kaveenkumar/SmartAgriculture/PPT Files/SA BLOCK DIAGRAM.pptx

INTERNET

USB

INPUT
SENSOR PORTS

RTC

RELAY

SIM900
GSM MODULE

16x2 LCD DISPLAY

ARM CORTEX M0

TARANG F4 ZIGBEE MODULE

Serial
Debugger

Opto
Coupler

POWER MANAGEMENT

INPUT SUPPLY
