kaveenkumar/SmartAgriculture/PPT Files/SA.pptx

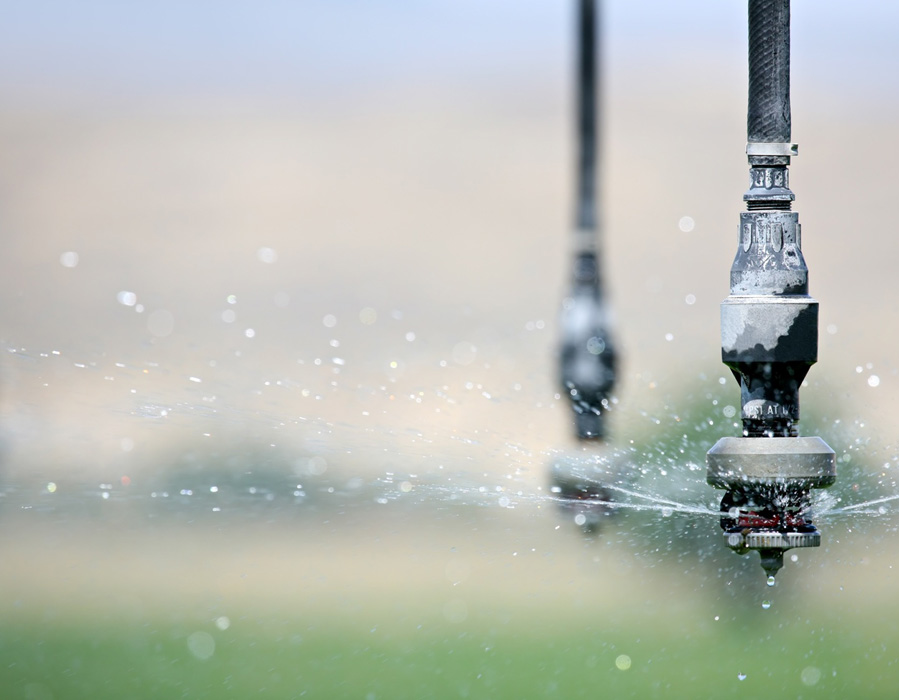
[picture p43: figure]

B.M.S COLLEGE OF ENGINEERING
Basavanagudi, Bangalore - 560 019, Karnataka, India
DEPARTMENT OF ELECTRONICS & OMMUNICATION

PROJECT PRESENTATION ON
“PRECISION AGRICULTURE”

1. Hemantha Gowda C.V. - 1BM11EC406 3. NIKHILESH.R - 1BM09IT017
2. KIRAN.M - 1BM09IT014 4. S.M.SALMAN - 1BM09IT025

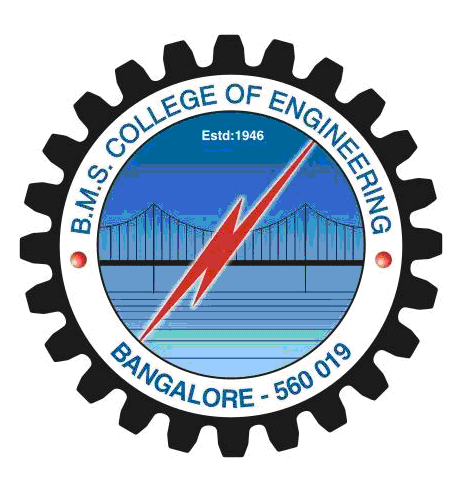
[picture p44: figure]

Project By:

## HISTORY

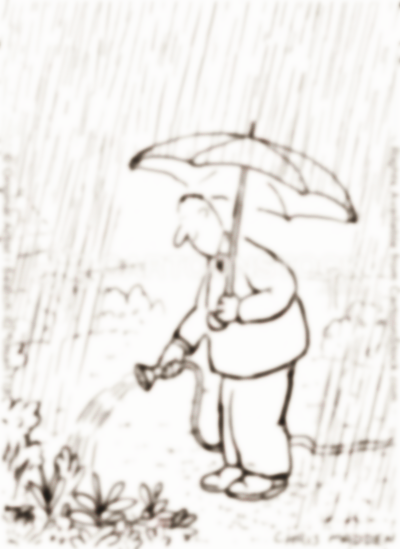
[picture p45: figure]

Agriculture being the Indian economy's strong-hold unfortunately suffers for the carelessness of its cultivators. Its high time we realized our responsibilities & worked towards the upliftment of the society.

## WHY?

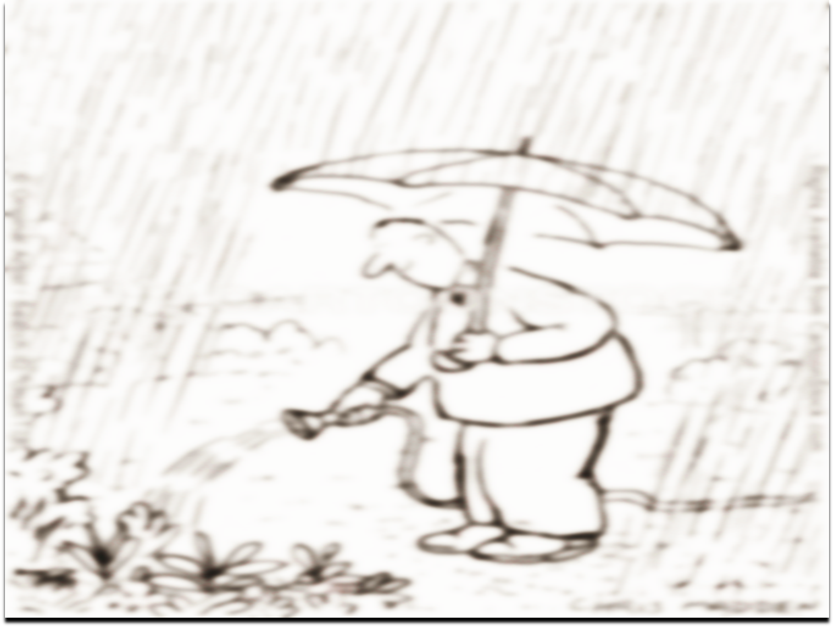
[picture p46: figure]

No remote Data Acquisition System in the present world is perfect until it remains effective and lasts for a pre-determined amount of time. The proposed Low Power Data Acquisition system proves to be advantageous in both the degrees.

## Slide 4

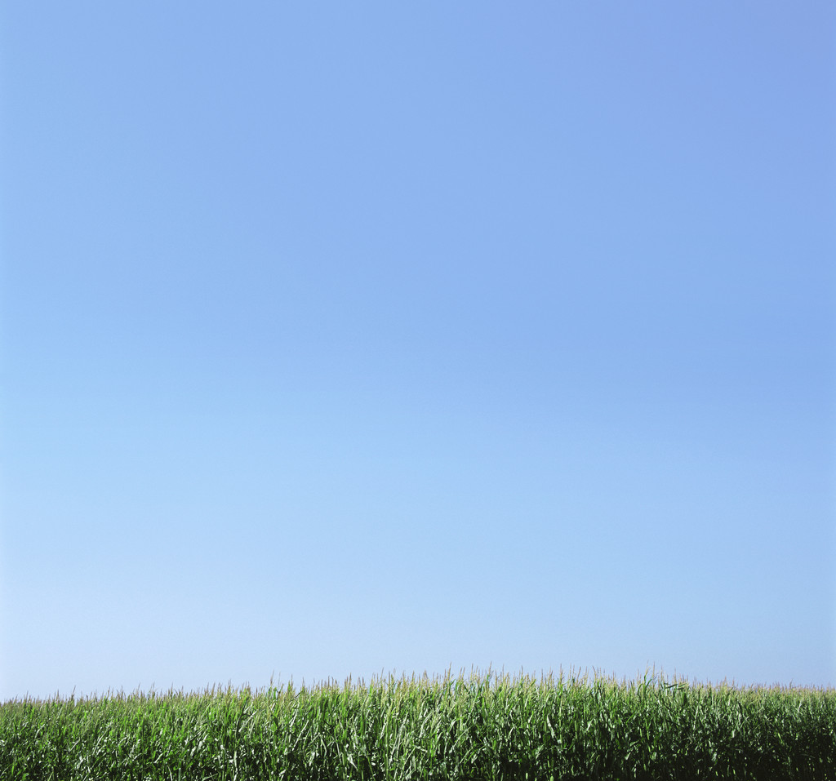
[picture p47: figure]

BLOCK DIAGRAM OVERVIEW

REMOTE
STATION

REMOTE
STATION

REMOTE
STATION

BASE
STATION

GPRS

SERVER

REMOTE
STATION

REMOTE
STATION

## Slide 5

BASE STATION

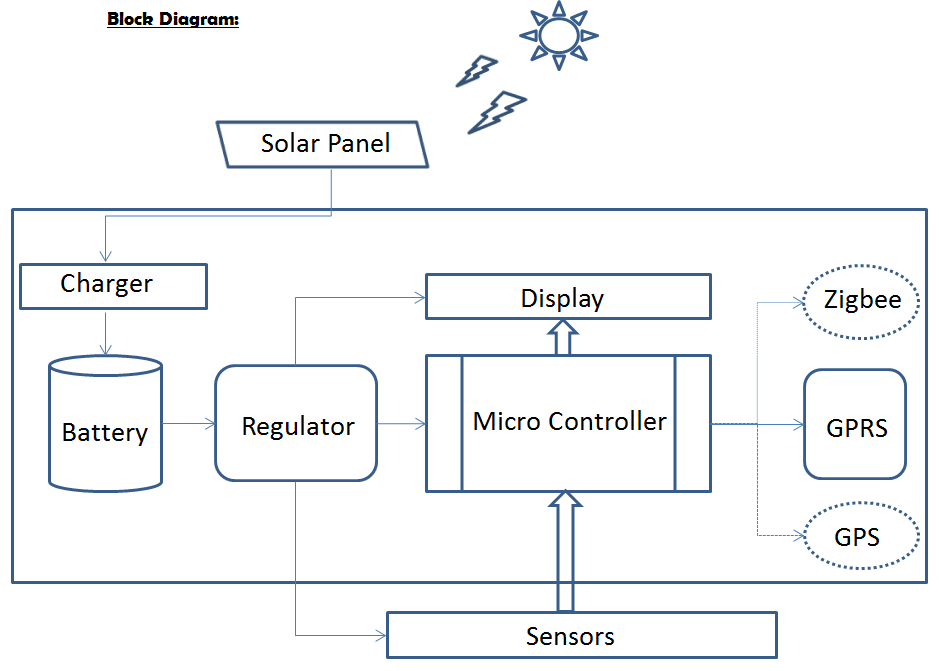
[picture p48: figure]

## COMPONENTS EMPLOYED

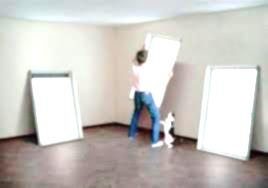
[picture p49: figure]

- ARM Cortex M0
- SIM900
- Relay & Opto-Coupler
- 16x2 Display
- Sensors
- Solenoid Valve
- Misc.

## PROS & CONS

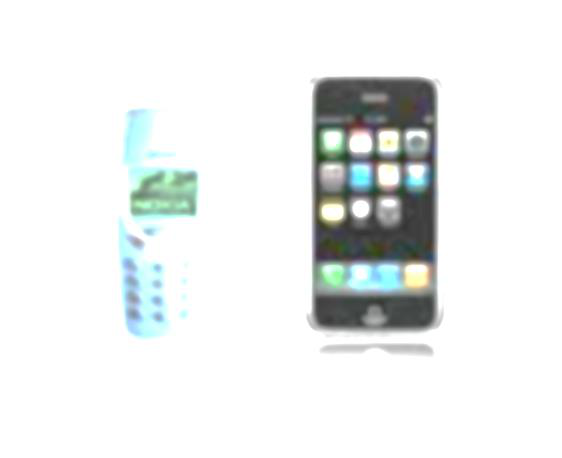
[picture p50: figure]

- Low power
- More advantages
- Less disadvantages

## Conclusion

Mutual investments are subject to market risk. Please read the offer documents carefully before investing.!
