kaveenkumar/SmartAgriculture/PPT Files/Smart Agriculture ppt.pptx

SMART AGRICULTURE

By

Technology At Farms…

Kaveen
Prathap
Nikhil
Hemanth

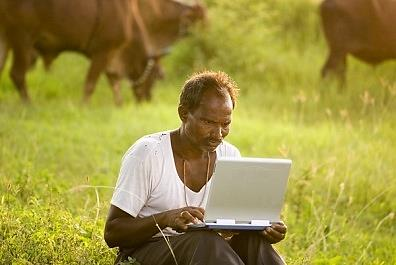
[picture p51: figure]

Guide

Harish V Mekali

## Slide 2

Why?

Optimum Water, More Yield…

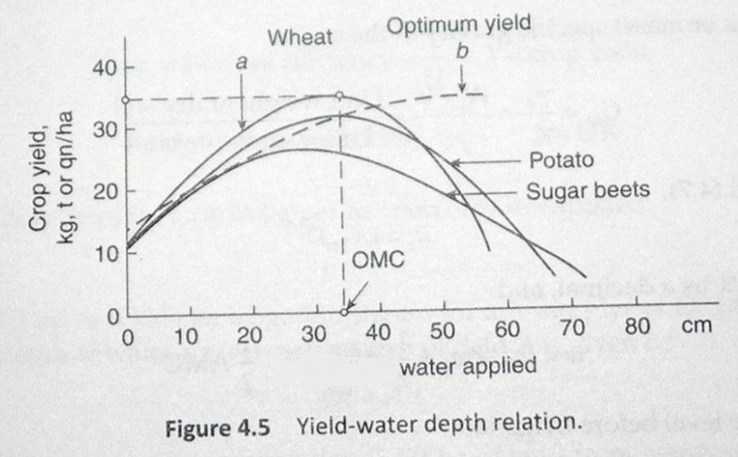
[picture p52: figure]

## Slide 3

Initialization…

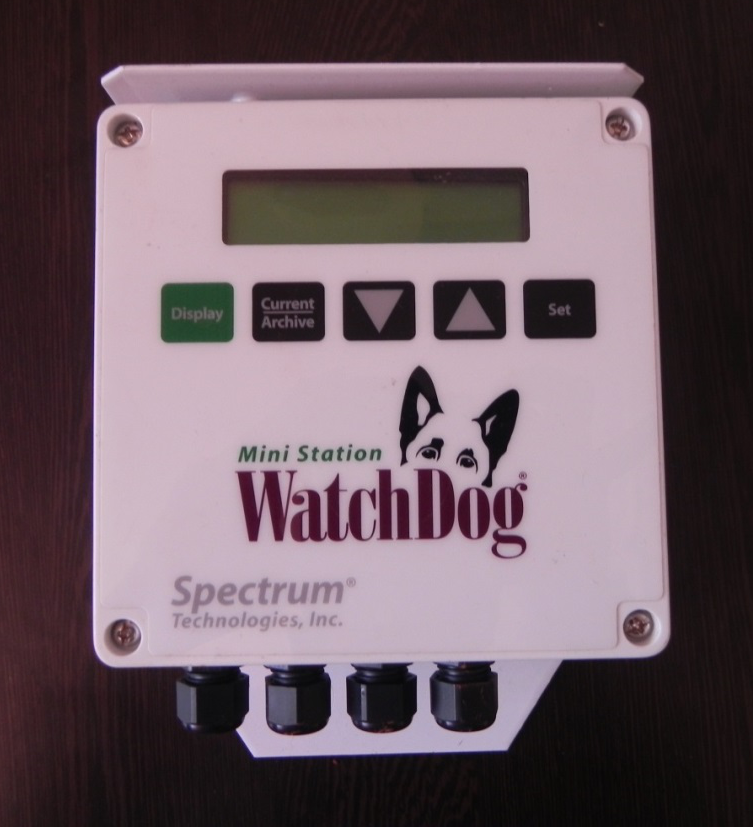
[picture p53: figure]

WatchDog

Sensors
4 Soil moisture sensors (SM100)

Data logger
Exclusive LCD Display confirms logger operation and provides current sensor readings. 0

Data transfer
USB to Serial for connecting to your Laptop

## Slide 4

Improvisation…


Base end

Weather Monitoring
system

Sensor values read

Read values sent

Received values at the user’s hands


User end

Temp:29⁰C SM:25% ST:18⁰C Lum:100lux RH:20%

SMS Format

## Slide 5

Conceptual Block

REMOTE
STATION

REMOTE
STATION

REMOTE
STATION

BASE
STATION

GPRS

SERVER

REMOTE
STATION

REMOTE
STATION

## Slide 6

Base Station…

Battery

Internet

––––

GPRS

Relay

Display

Sensors

ARM Cortex

Memory

## Slide 7

Components…

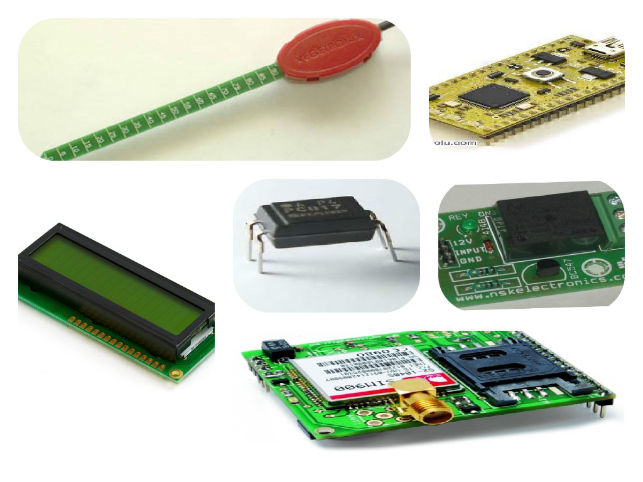
[picture p54: figure]

## Slide 8

Remote Data Acquisition…


The web-link is: http://bmsems.org/new

## Slide 9

Welcome Page…

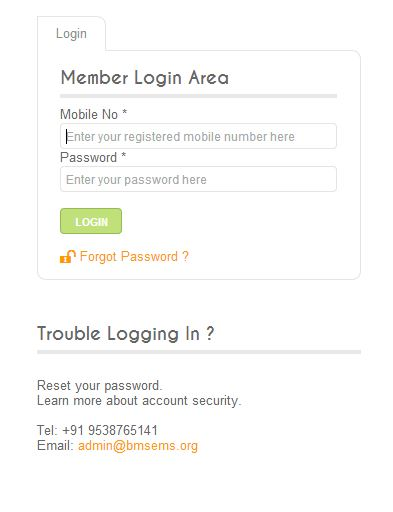
[picture p55: figure]

- Each user is provided with his own distinct ID & a secret password through which he can access the required data.

This way both authentication of the identity and confidentiality of the data is maintained

## Slide 10

User Page…


The user has to login to the website as a member to access the data or use the website to read the parameter he wishes to get a hold on. For this he has to obtain the permission from the administrator.

## Slide 11

Data Page..


Initially we enter the information about soil type, crop and the date of plantation. This information is automatically updated to the database and based on this information our device controls the situation.

## Slide 12

Graph

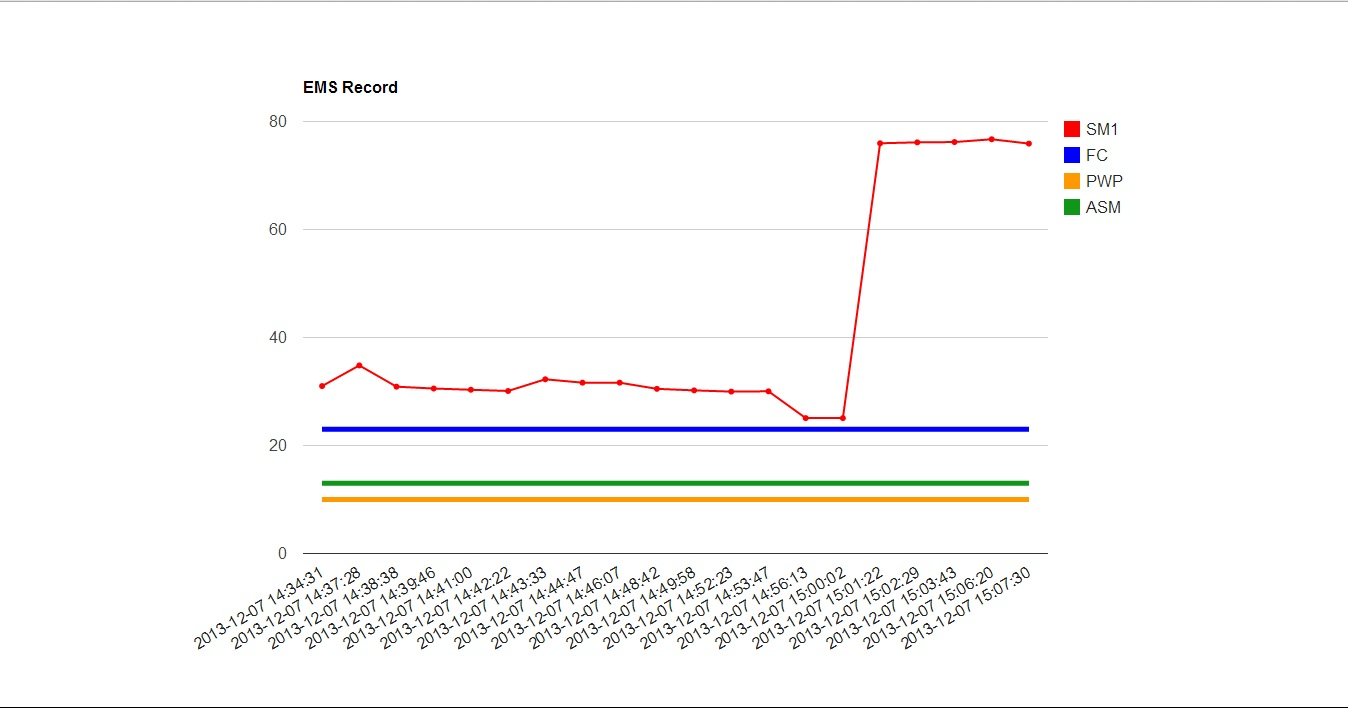
[picture p56: figure]

A graph displays the various sensor values employed, in detail and the output crop details along with the current battery percentage remaining.

## Slide 13

Excel Spreadsheet…


The various sensor data are collectively stored in an excel sheet which can be used later to analyse. The excel files are maintained in an archive format so that less capacity holds maximum amount of information.

## Slide 14

Working Model…

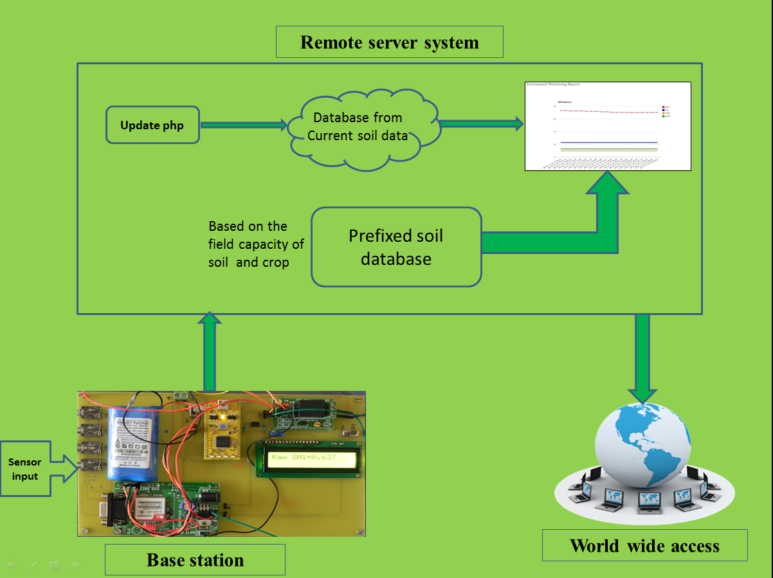
[picture p57: figure]

## Demo

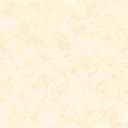
[picture p58: figure]

## Slide 16

Conclusion

We proudly propose this idea to enhance the well-being of the farmers who reside at remote places to obtain the knowledge of their fields and crop information.
We feel glad to conclude that we have touched an effort of few technological fields, for sensible information management, making use of modern wireless communication such as GPRS

## Slide 17

Recognition

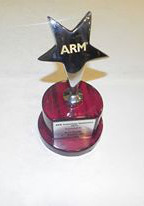
[picture p59: figure]

2nd runner up in the ARM Symposium held at Le Meridian, Bangalore in the year 2013.

## Slide 18

Future Work

Solar Panel

- Low power up gradation
- Autonomous power management system
- Creating the wireless sensor network
- Real tine implementation in the fields.

––––

Charger Unit

Display

Zigbee

Battery

Regulator

ARM Cortex

GPRS

GPS

Sensors

## Slide 19

Sponsors…

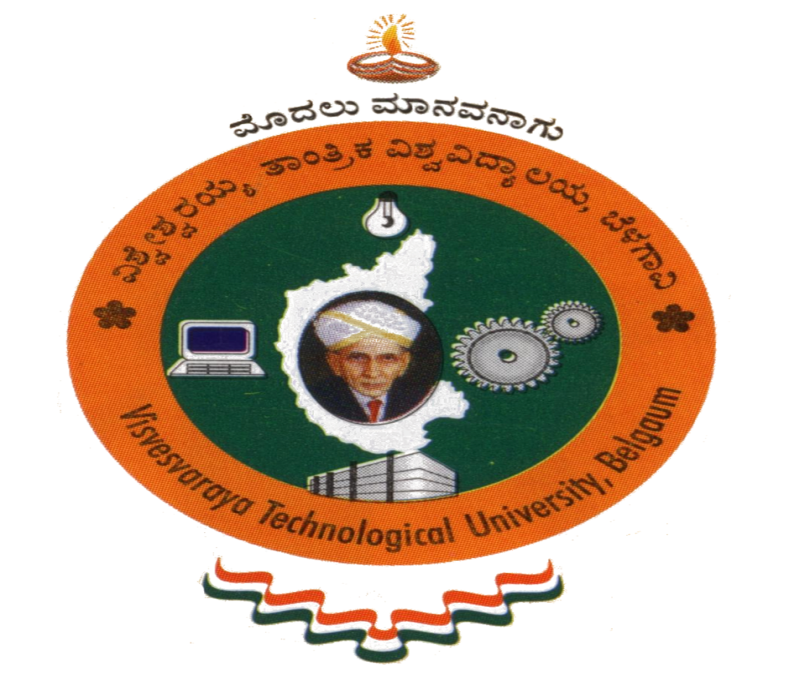
[picture p60: figure]
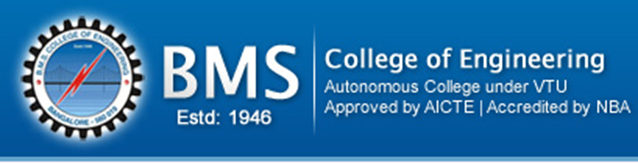
[picture p61: figure]

TEQIP

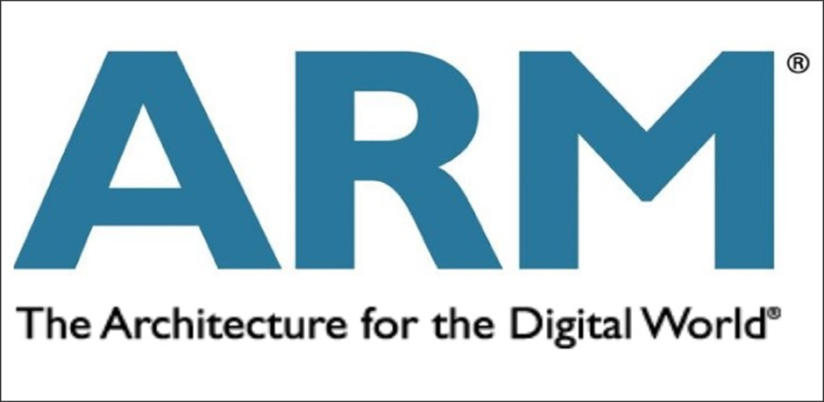
[picture p62: figure]

## Slide 20

Thank You

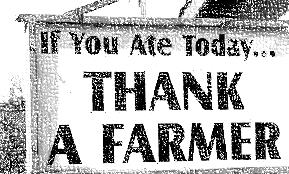
[picture p63: figure]
