kaveenkumar/SmartAgriculture/Word Files/First Page_final.docx

PROJECT REPORT

ON

“TITLE OF THE PROJECT”

Submitted in partial fulfillment of the requirements for the award of degree of

BACHELOR OF ENGINEERING

IN

ELECTRONICS AND COMMUNICATION ENGINEERING


VISVESVARAYA TECHNOLOGICAL UNIVERSITY, BELGAUM

SUBMITTED BY:

Chetan Kumar 1BM08EE012

Raghavendra K 1BM08EE025

Manjunath Adiga 1BM08EE033

Rahul Kishan P 1BM08EE051

Under the Guidance of,

INTERNAL GUIDE EXTERNAL GUIDE


Department of Electronics and Communication Engineering

B.M.S COLLEGE OF ENGINEERING

(Autonomous College Affiliated to Visvesvaraya Technological University, Belgaum)

Bull Temple Road, Basavanagudi, Bangalore-560019
