kaveenkumar/SmartAgriculture/Word Files/SA SC.docx

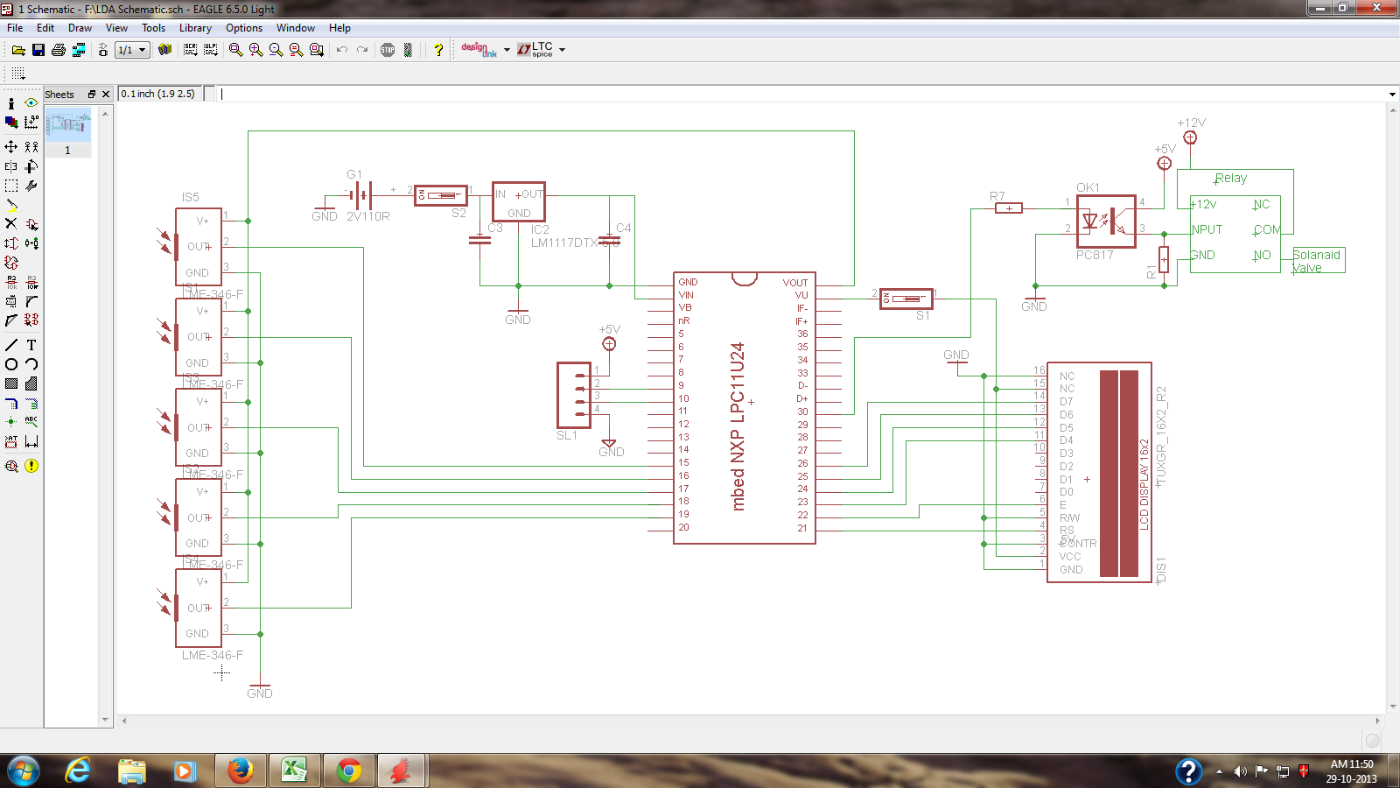
[picture p104: figure]
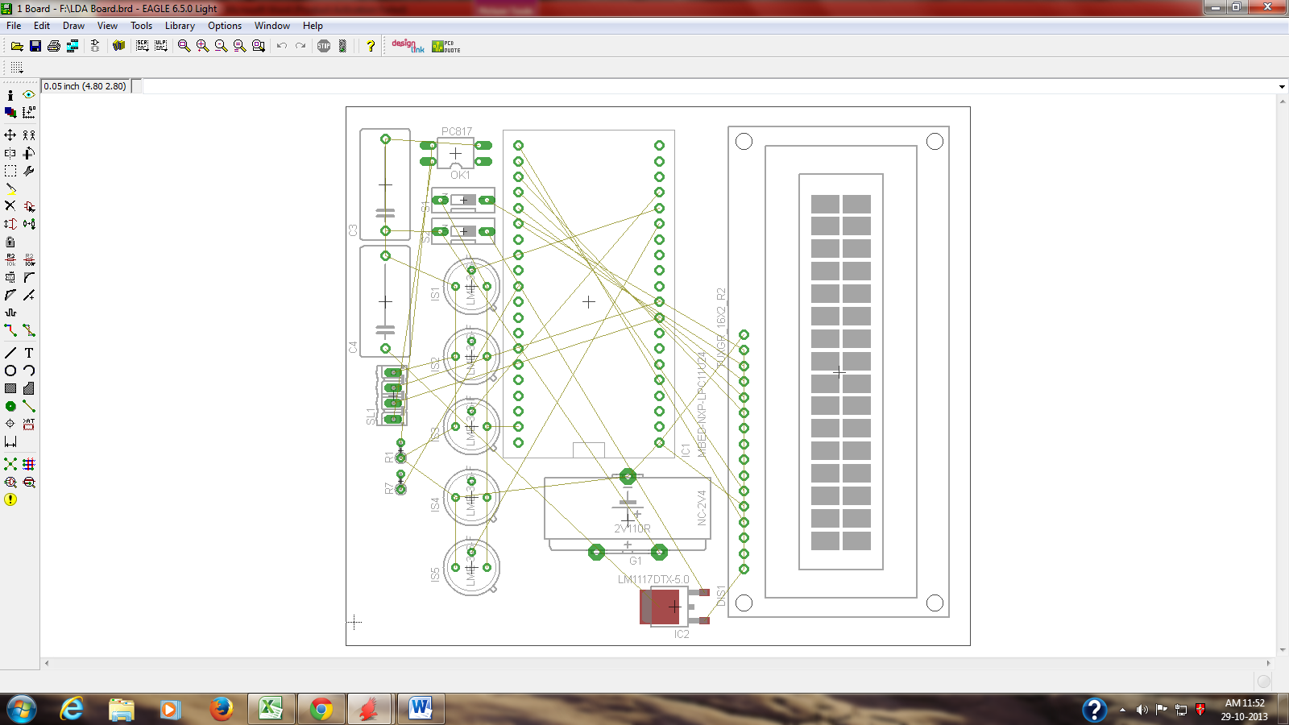
[picture p105: figure]
