kaveenkumar/SmartAgriculture/Images/1bmsce.jpg

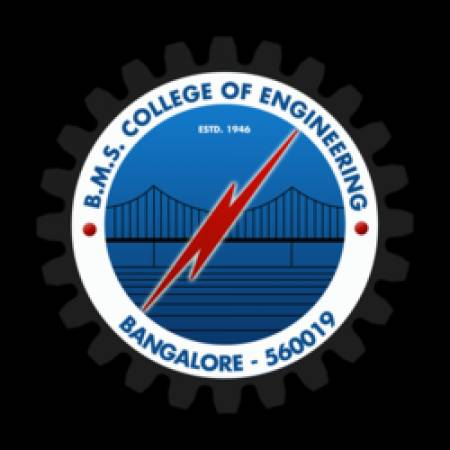
Images/1bmsce.jpg
