kaveenkumar/SmartAgriculture/Images/5.JPG

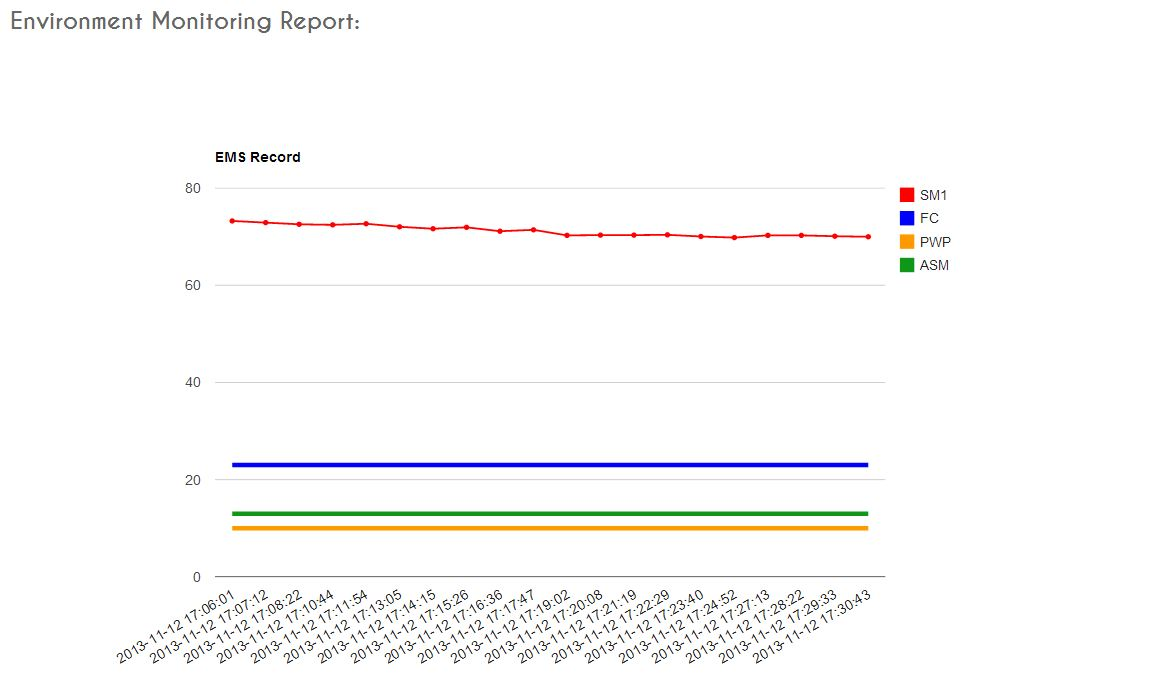
Images/5.JPG
