kaveenkumar/SmartAgriculture/Images/44898_Fotolia_1152136.jpg

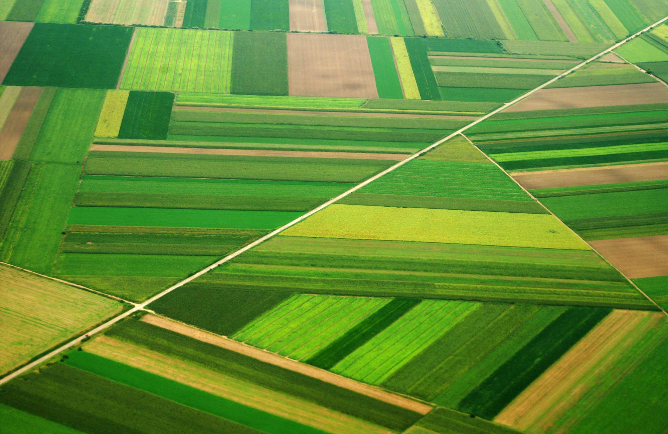
Images/44898_Fotolia_1152136.jpg
