kaveenkumar/SmartAgriculture/Images/539744_10200658317091345_661823956_n.jpg

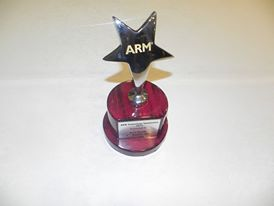
Images/539744_10200658317091345_661823956_n.jpg
