kaveenkumar/SmartAgriculture/Images/3420721-162307-fresh-spring-green-grass-natural-grass-texture.jpg

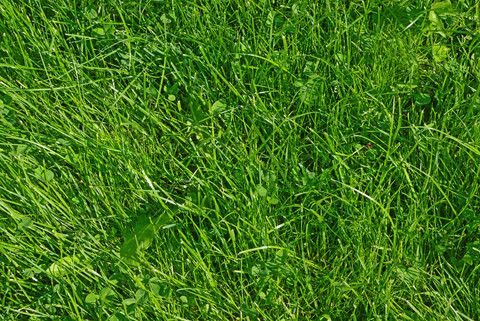
Images/3420721-162307-fresh-spring-green-grass-natural-grass-texture.jpg
