kaveenkumar/SmartAgriculture/Images/back2.jpg

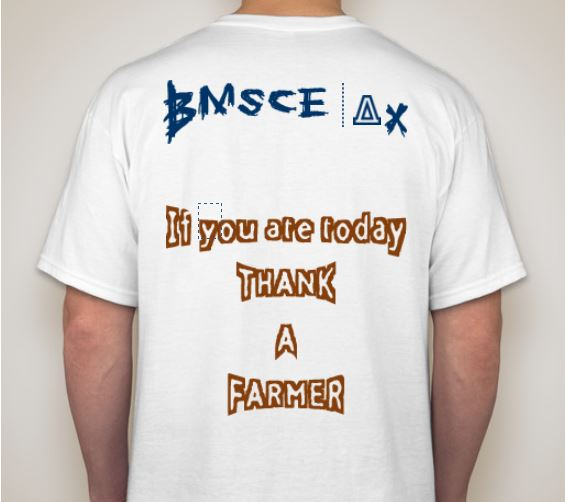
Images/back2.jpg
