kaveenkumar/SmartAgriculture/Images/back tee.jpg

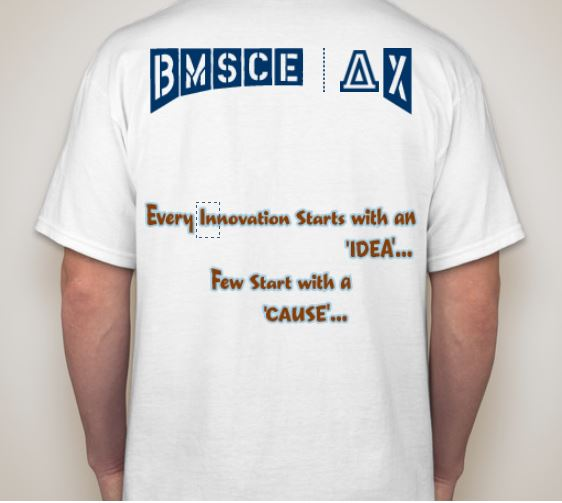
Images/back tee.jpg
