kaveenkumar/SmartAgriculture/Images/base.JPG

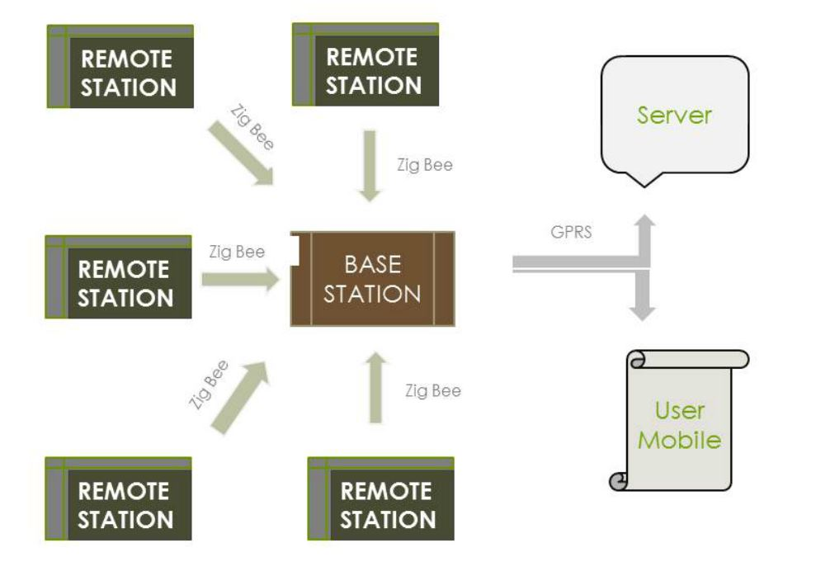
Images/base.JPG
