kaveenkumar/SmartAgriculture/Images/block diagram.JPG

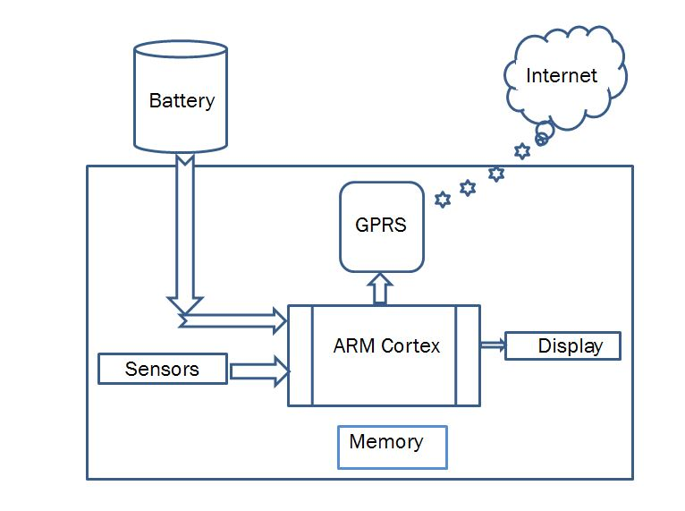
Images/block diagram.JPG
