kaveenkumar/SmartAgriculture/Images/code_flow.JPG

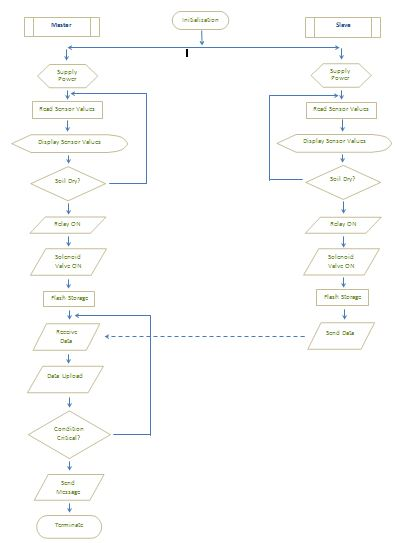
Images/code_flow.JPG
