kaveenkumar/SmartAgriculture/Images/download.jpg

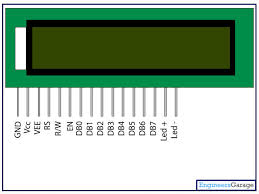
Images/download.jpg
