kaveenkumar/SmartAgriculture/Images/front tee.jpg

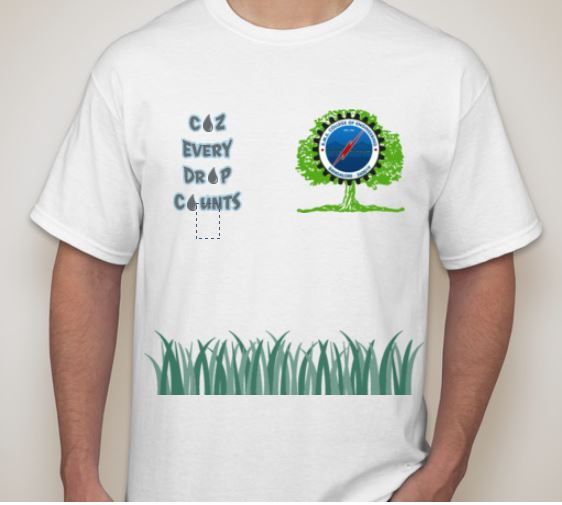
Images/front tee.jpg
