kaveenkumar/SmartAgriculture/Images/Govt-Policy-Illustration.jpg

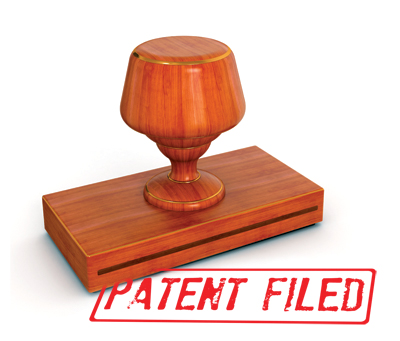
Images/Govt-Policy-Illustration.jpg
