kaveenkumar/SmartAgriculture/Images/graph1.JPG

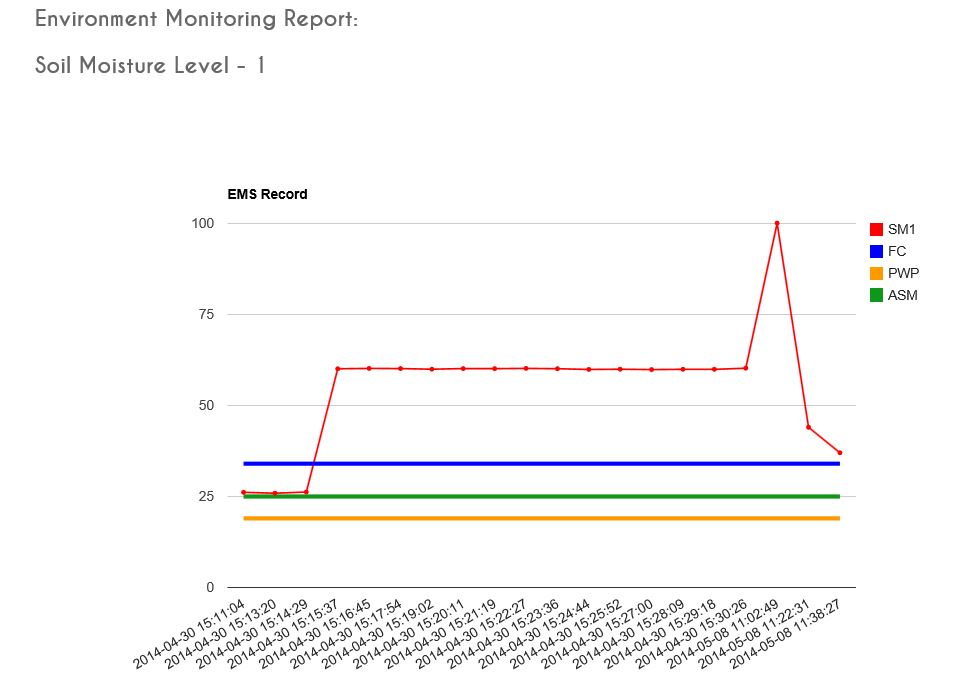
Images/graph1.JPG
