kaveenkumar/SmartAgriculture/Images/graph_new.PNG

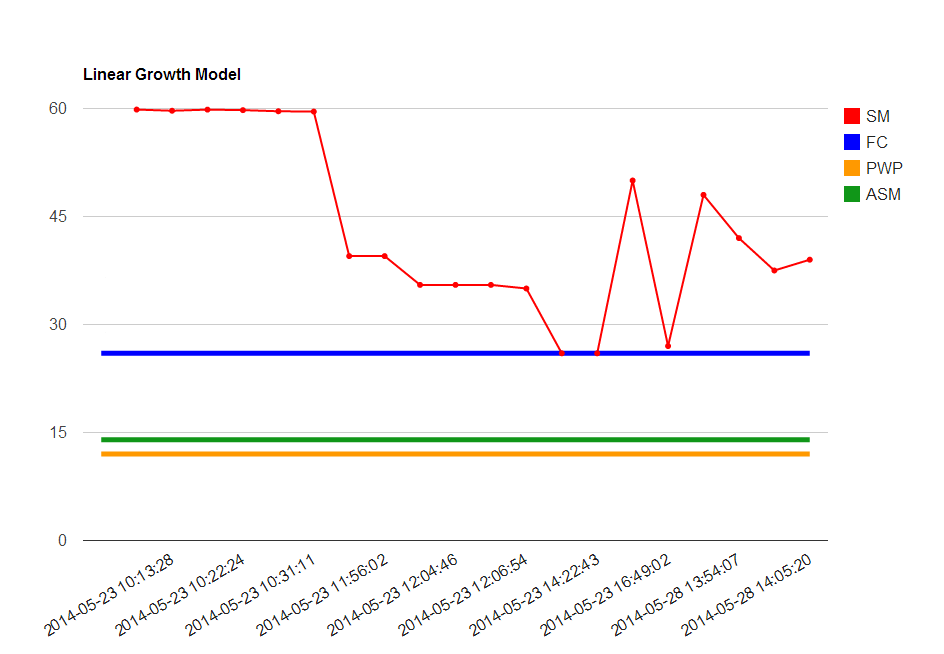
Images/graph_new.PNG
