kaveenkumar/SmartAgriculture/Images/GS.jpg

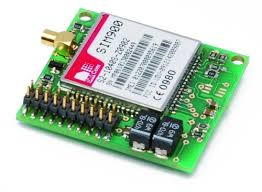
Images/GS.jpg
