kaveenkumar/SmartAgriculture/Images/Harishm.jpg

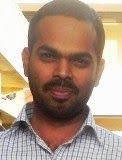
Images/Harishm.jpg
