kaveenkumar/SmartAgriculture/Images/if-you-ate-today-thank-a-farmer.png

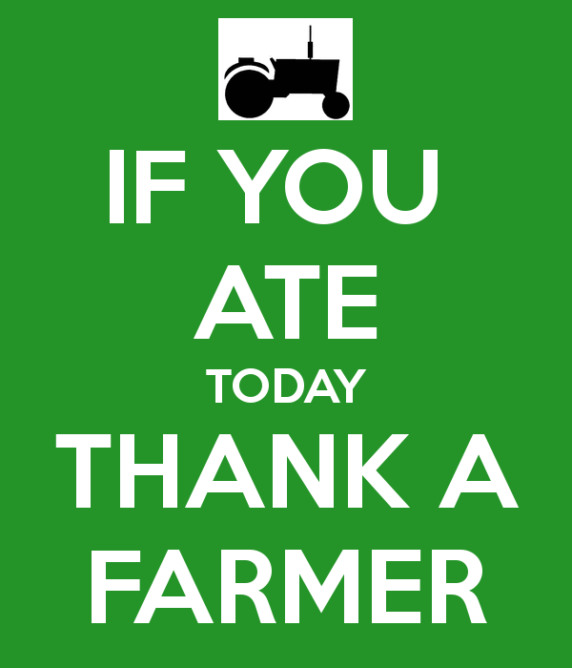
Images/if-you-ate-today-thank-a-farmer.png
