kaveenkumar/SmartAgriculture/Images/image.jpeg

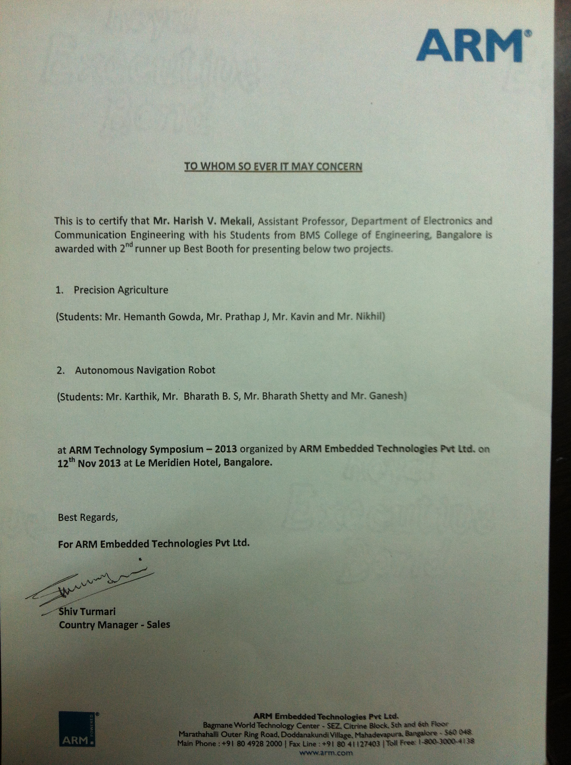
Images/image.jpeg
