kaveenkumar/SmartAgriculture/Images/IMG_2141.PNG

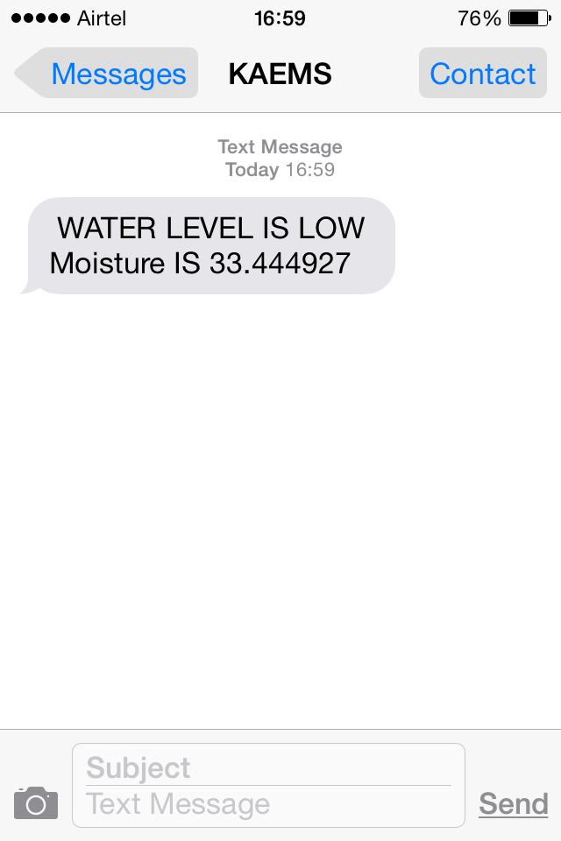
Images/IMG_2141.PNG
