kaveenkumar/SmartAgriculture/Images/left.jpg

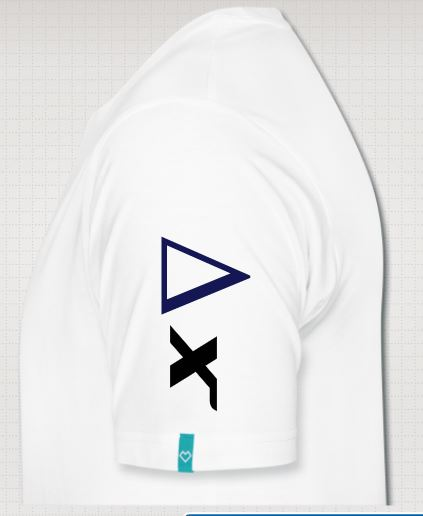
Images/left.jpg
