kaveenkumar/SmartAgriculture/Images/PA Communication.jpg

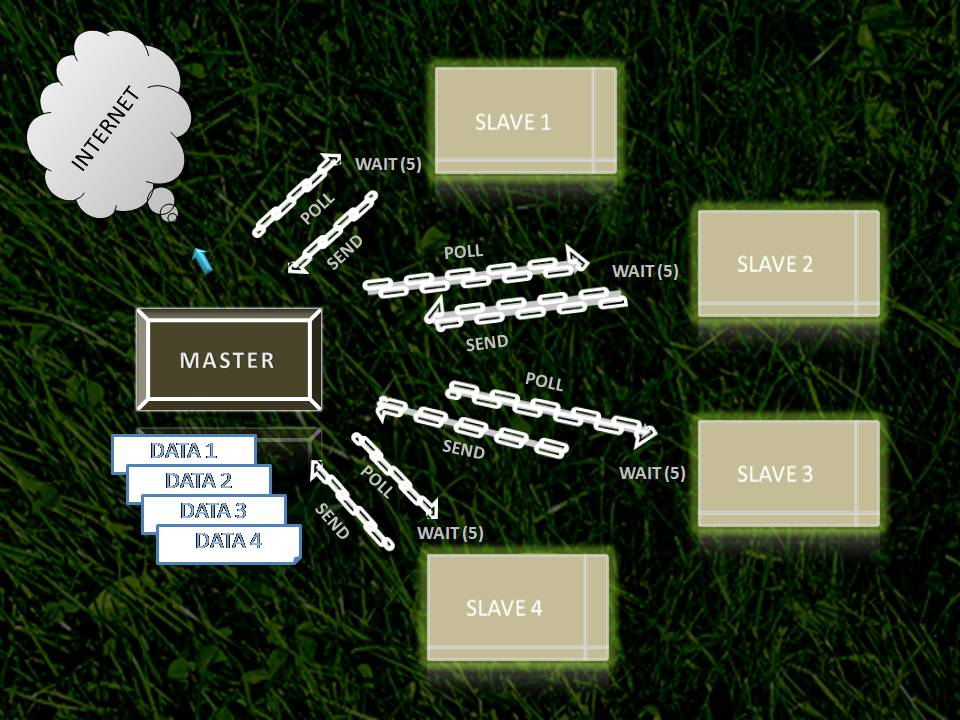
Images/PA Communication.jpg
