kaveenkumar/SmartAgriculture/Images/PROJECTINBOX.jpg

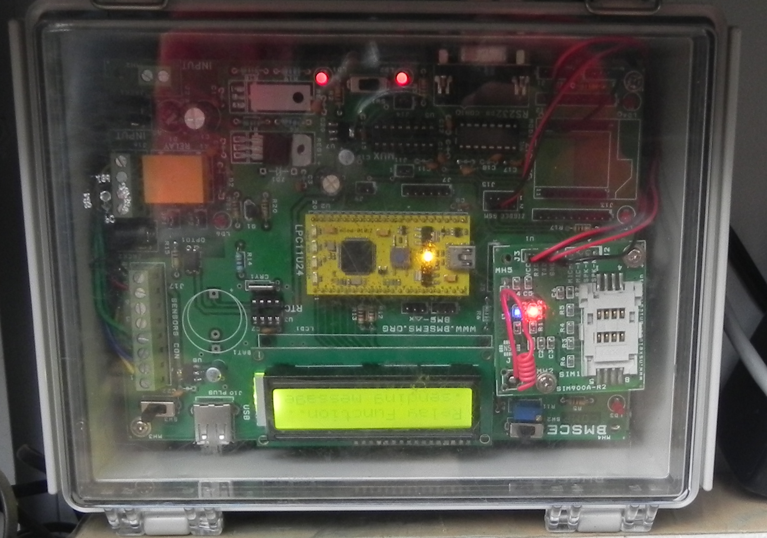
Images/PROJECTINBOX.jpg
