kaveenkumar/SmartAgriculture/Images/relay.jpg

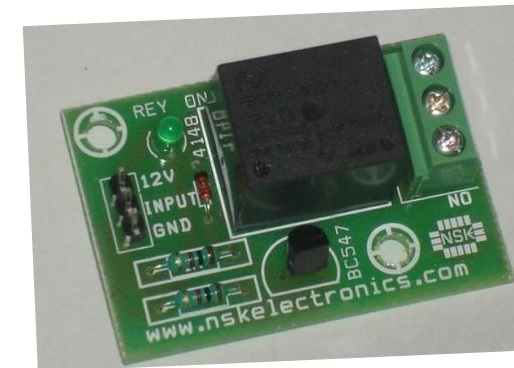
Images/relay.jpg
