kaveenkumar/SmartAgriculture/Images/right.jpg

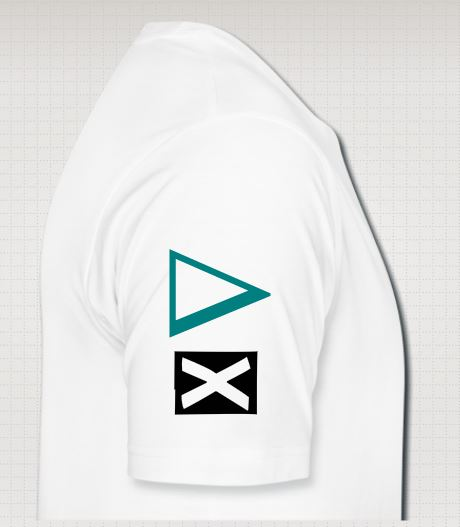
Images/right.jpg
