kaveenkumar/SmartAgriculture/Images/rtc2.JPG

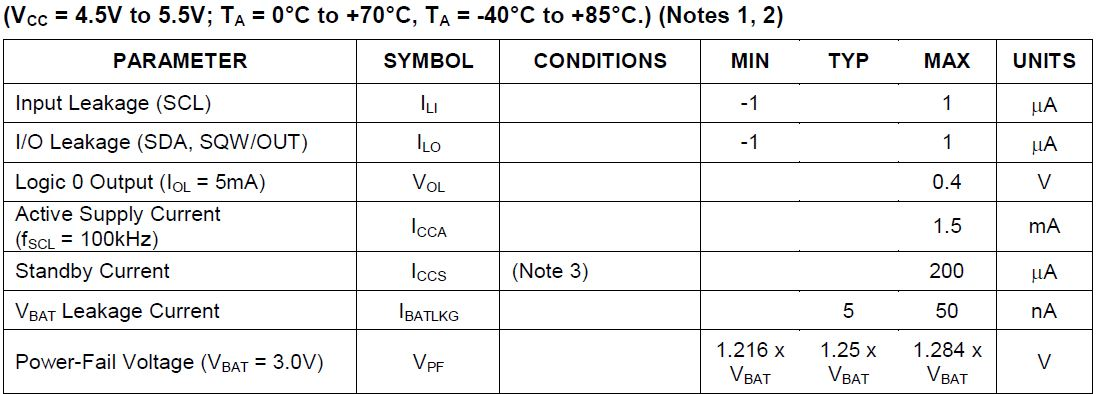
Images/rtc2.JPG
