kaveenkumar/SmartAgriculture/Images/rtc3.JPG

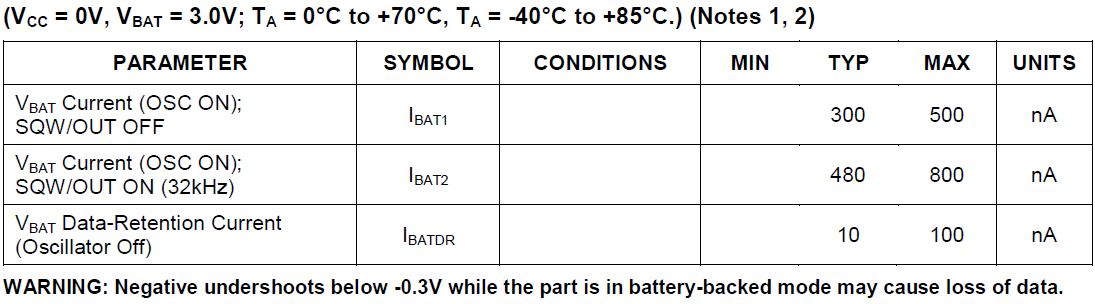
Images/rtc3.JPG
