kaveenkumar/SmartAgriculture/Images/rtc4.JPG

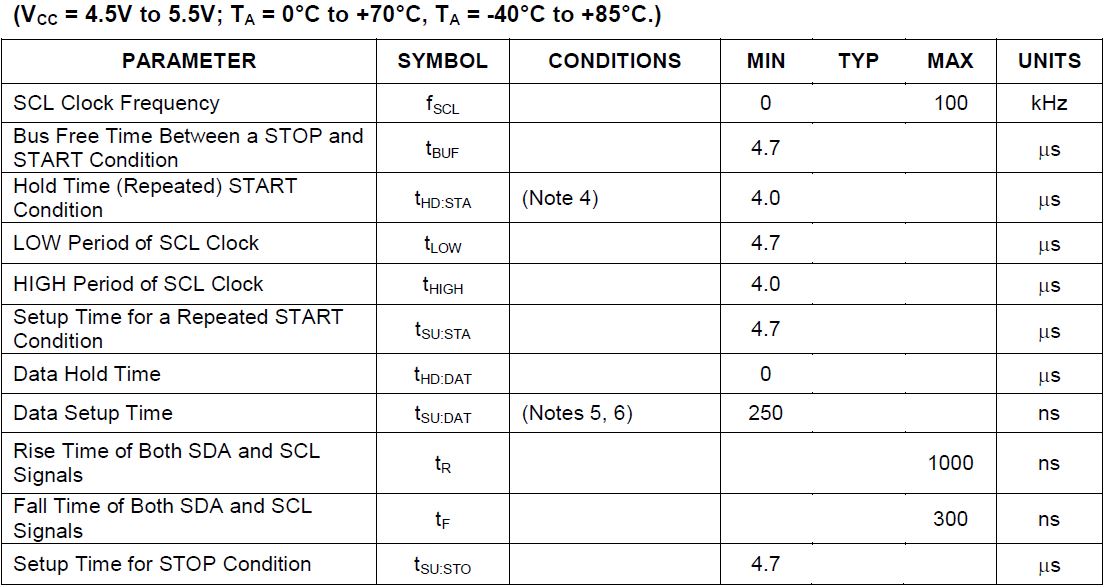
Images/rtc4.JPG
