kaveenkumar/SmartAgriculture/Images/RTC.JPG

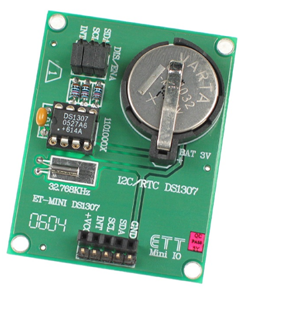
Images/RTC.JPG
