kaveenkumar/SmartAgriculture/Images/SA BLOCK DIAGRAM (2).jpg

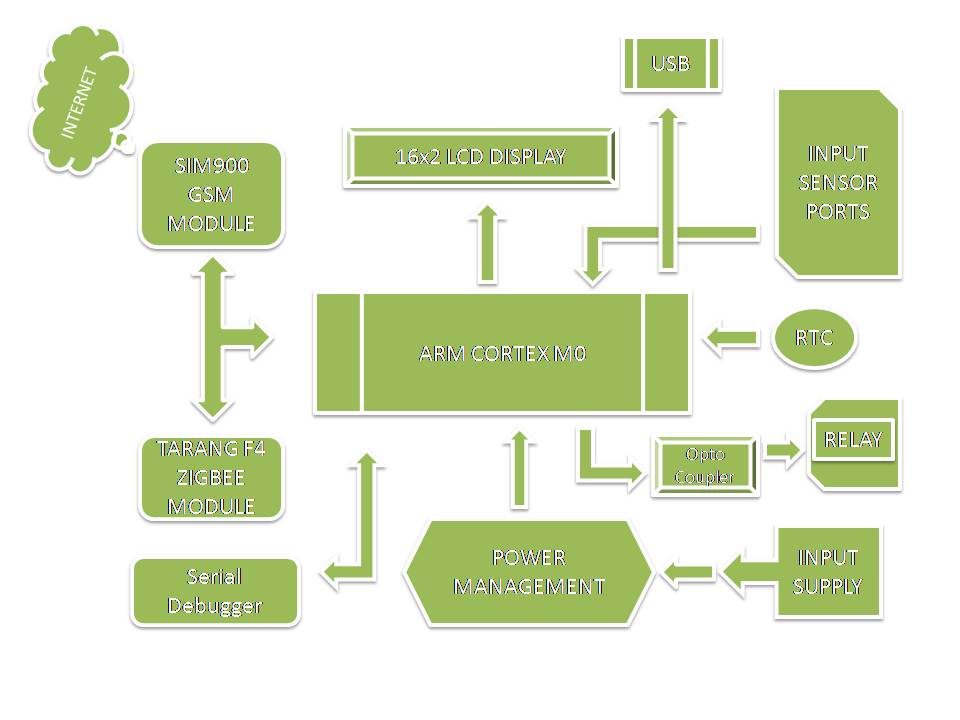
Images/SA BLOCK DIAGRAM (2).jpg
