kaveenkumar/SmartAgriculture/Images/SA Block Diagram.jpg

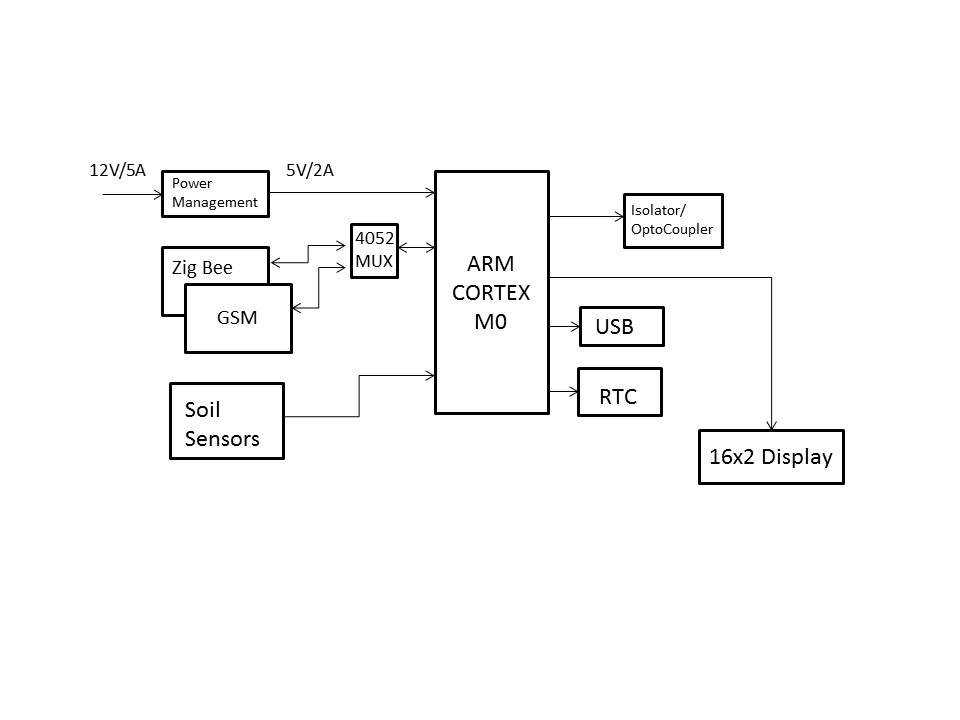
Images/SA Block Diagram.jpg
