kaveenkumar/SmartAgriculture/Images/tarang_AC.JPG

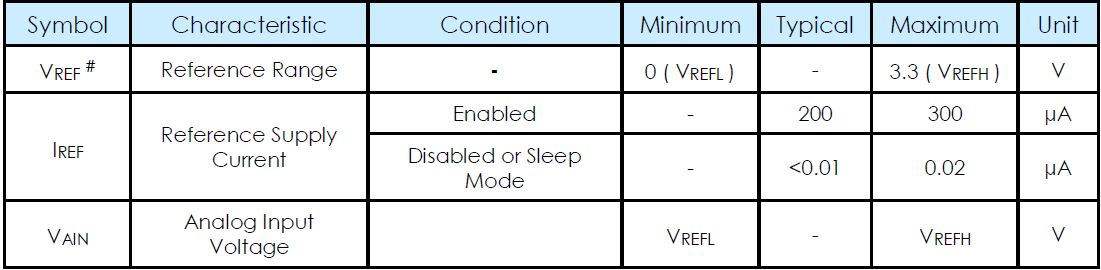
Images/tarang_AC.JPG
