kaveenkumar/SmartAgriculture/Images/tarang_DC.JPG

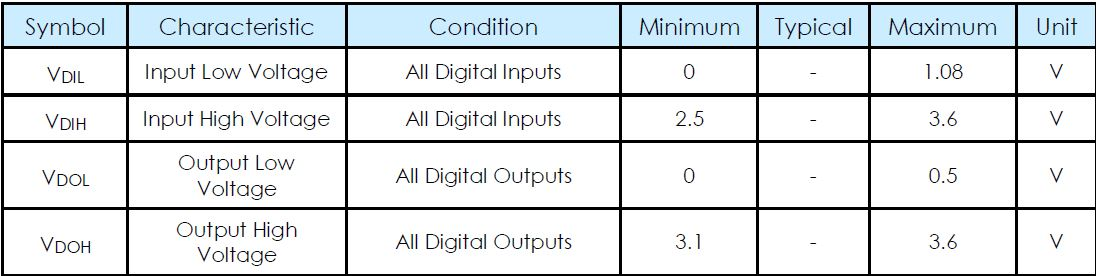
Images/tarang_DC.JPG
