kaveenkumar/SmartAgriculture/Images/tarang_general.JPG

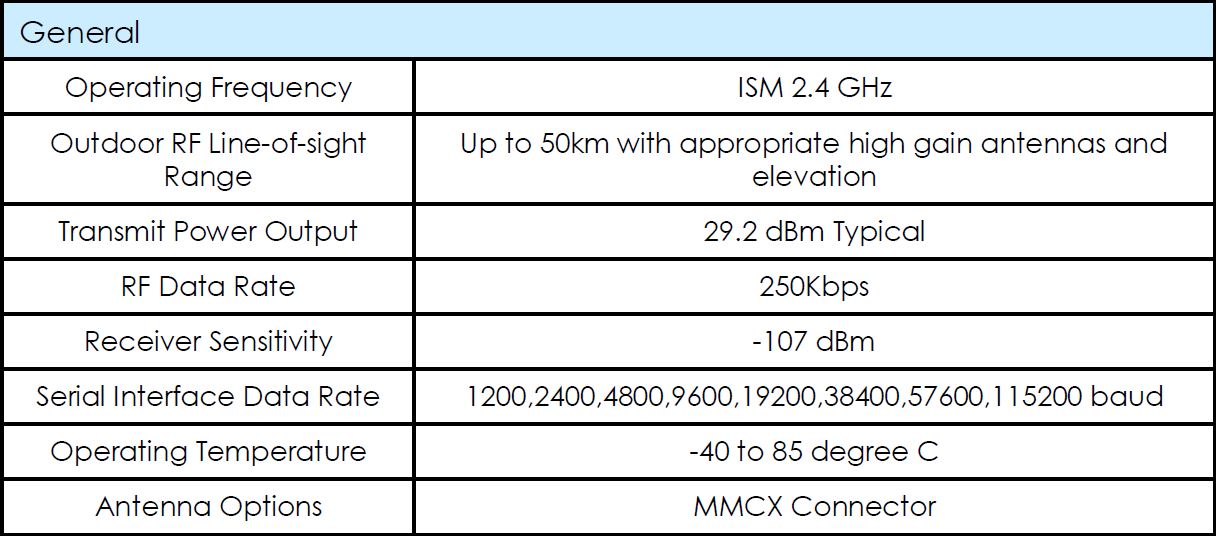
Images/tarang_general.JPG
