kaveenkumar/SmartAgriculture/Images/tarang_modem.JPG

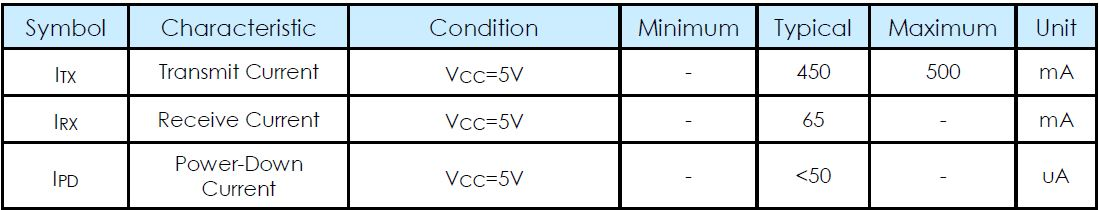
Images/tarang_modem.JPG
