kaveenkumar/SmartAgriculture/Images/tarang_network.JPG

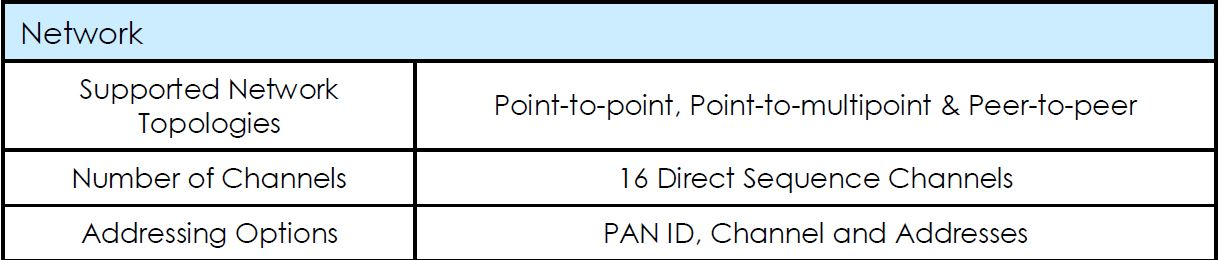
Images/tarang_network.JPG
