kaveenkumar/SmartAgriculture/Images/tarang_power.jpg

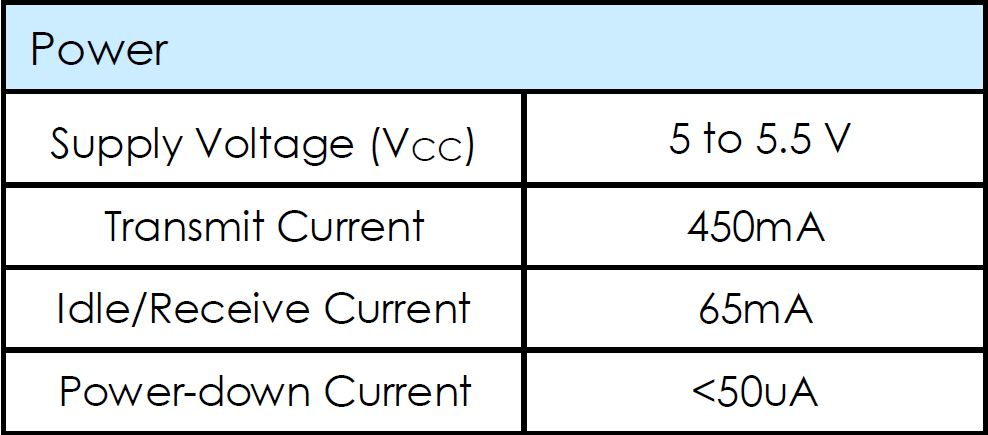
Images/tarang_power.jpg
