kaveenkumar/SmartAgriculture/Images/TEQP.jpg

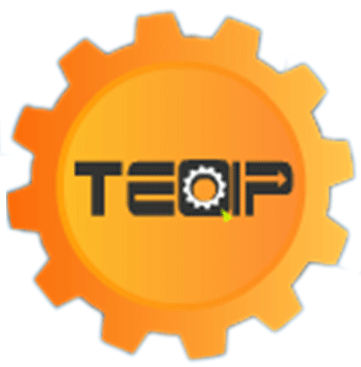
Images/TEQP.jpg
