kaveenkumar/SmartAgriculture/Images/Thank-a-farmer-pic.jpg

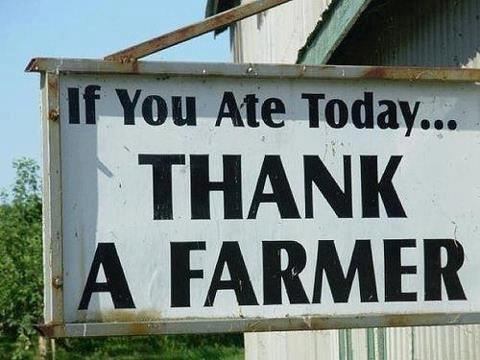
Images/Thank-a-farmer-pic.jpg
