kaveenkumar/SmartAgriculture/Images/Untitled.jpg

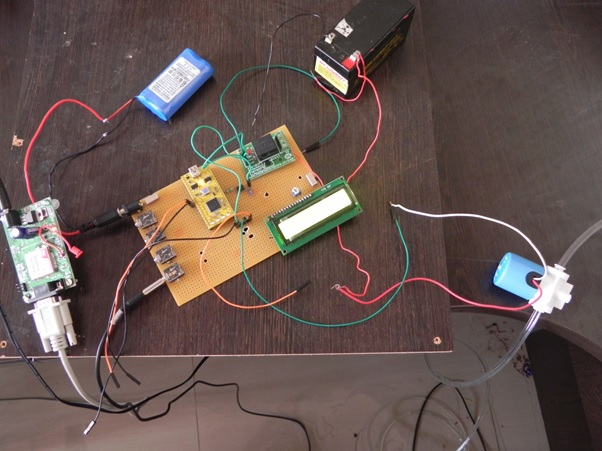
Images/Untitled.jpg
