kaveenkumar/SmartAgriculture/Images/vehicle board.jpg

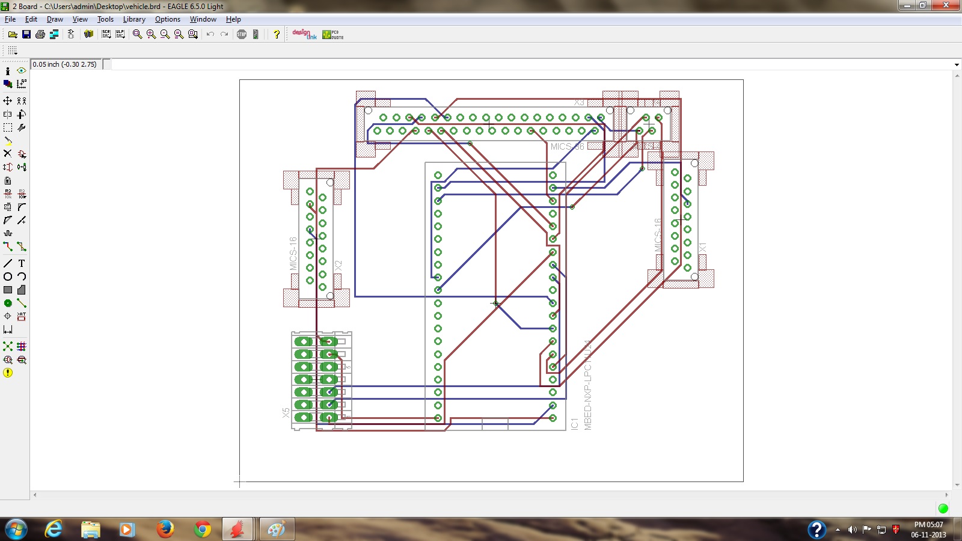
Images/vehicle board.jpg
