kaveenkumar/SmartAgriculture/Images/wms rx.jpg

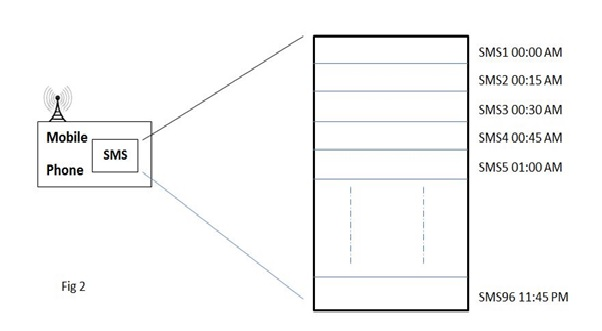
Images/wms rx.jpg
