kaveenkumar/SmartAgriculture/Images/wms sms.jpg

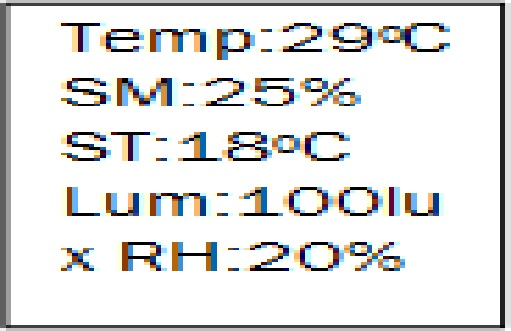
Images/wms sms.jpg
